fionnf/ember/hardware/ember/README.md

# EM-15 rev I — KiCad project

**Ember · EM-15 rev I · © 2026 Fionn Ferreira**
<https://github.com/fionnf/ember>

Generated from [`../../docs/hardware/README.md`](../../docs/hardware/README.md).
Open `fl11.kicad_pcb` with KiCad 9 or 10.

## What changed

**rev B** moved the electronics off the end of the strip into a rear bulge at the middle, so
the USB-C plugs in from the back. **rev C** moved the touch terminals there too: the pad is
now a snap-off section *beside* the bulge, not a tab at the far end.

```
   x=0                                              187
   |<---------- 11 x SK6812 RGBW, unbroken --------->|
   +--------------------------------------------------+
   | (1)(2)(3)(4)(5)(6)(7)(8)(9)(10)(11)  y = 11.000  |
   +----------------+--------------+---+--------------+
        y=20        |  ELECTRONICS |sn |  TOUCH PAD   |
                    |  MCU, power  |ap |  PAD_S       |
                    |  USB-C under |   |  PAD_G       |
              x=72  +--------------+---+--------------+ x=145
                         y=48    x=120 (break + J2/J3)
```

Every wire now leaves the lamp from one place. The board also got **smaller**:

| | rev A | rev B | rev C |
|---|---|---|---|
| Outline | 282 × 20 | 228 × 20 + 48 × 28 | **187 × 20 + 48 × 28 + 25 × 28** |
| Area | 5640 mm² | 5904 mm² | **5784 mm²** (+2.6 % vs A, −2.0 % vs B) |
| SENSE run | 195 mm | ~70 mm | **~13 mm** |
| SENSE crosses the LED data channel | no | yes, once | **no** |

**The real win is SENSE.** §7.5 calls touch "the least-certain subsystem in this design". In
rev A and B the sense line was a long high-impedance run down a strip carrying a 0.89 A
switching rail. In rev C it never leaves the bulge, sits inside the bulge's GND pour — which
*is* the guard — and never crosses the LED data channel. The guarded y=18.6 lane rev B needed
is gone entirely, and so is the awkward climb at x=188.

Deleting the end tab also removed the 31 mm tab, the gap, and the strip's break slot.

**Cost.** Still one bottom-side part (J1), so the second-setup charge stands at roughly
**+$0.63/unit at qty 100**. The outline is a T with a notch, so the 6-up panel still needs
re-nesting and re-quoting.

## rev I — TTP223 module, and the etched sensor is gone

The biggest simplification in the whole design. A **TTP223-class module plugs into J4**
(pin order **IO / VCC / GND**) and does the sensing, which deletes:

- the etched comb electrodes and their whole geometry problem
- the snap-off pad section, the break line, the webs and both bridges
- R10's 4.7 MΩ (now 100 k, a value already on the BOM) — **the thinnest-stock line is gone**
- §7.5's entire uncertainty: the charge-time measurement, the per-unit threshold question,
  the overlay-thickness dependence, the "least-certain subsystem in this design" note

`touch.py` becomes a digital read instead of a timing loop.

**VCC is 3V3, not 5V, deliberately.** These modules drive their output rail-to-rail and the
ESP32-C3 is **not 5V tolerant** (3.6 V absolute max). At 3V3 the output is inherently safe,
and R7's 5.1 kΩ stays in series as belt and braces. `TS3/TS4/TS5` repeat the same three
signals as solder terminals for when no JST housing is to hand.

**Centred geometry.** The LED row sits square on the strip — **15.567 mm of headroom at each
end**, identical. The USB-C sits **dead centre of the bulge at x=98.0**; the module moved
aside to x=115 to make room, which puts its antenna keep-out at y 40.9–46.3 facing the free
y=52 edge, **23.9 mm** from the nearest LED copper against a rule of 8.

**Four screws**: two in the bulge, and one at **each end of the LED strip**, so the full
length is held down rather than just the electronics.

### Routing: complete

| | |
|---|---|
| **Unconnected component pads** | **0** |
| DRC errors | **0** |
| Board | 187 × 20 strip + 64 × 32 bulge, single-sided, 2 layer |
| BOM | 16 lines, 59 placements, 5 BASIC |

Pipeline: `build_fl11.py` places and netlists, `route_fl11.py` lays the pours and the nets
§7.9 insists on by hand, freerouting 2.3.0 finishes the rest through KiCad's Specctra
DSN/SES path, and `finish_routing.py` cleans up after it — width floor, 133 collision-checked
ground vias, solid ties, island removal, stray-pad joins.

## rev G — 15 LEDs, fully routed

**15 LEDs at 11.13333 mm pitch.** The lit zone stays at exactly **167.00 mm** — the lamp
length does not move — and worst-case current drops to **~1.69 A**, back under the 2 A PPTC
hold and inside a 2.4 A supply. F1 returns to the 2 A/4 A part. Both of the warnings rev F
carried (3 A supply, copper resized for 2.25 A) are withdrawn: at 1.69 A the §5.5 sizing
holds with margin.

**The LEDs are warm white.** `C5378724` is `SKC6812RGBW-**WS**` — the WS suffix is warm white.
The neutral-white part is `C5348912` (`-NW`) and would fight `BASE_WARM_WHITE = (0,0,0,200)`,
which is the whole basis of `colour.py`'s model. The BOM note says so explicitly.

### Routing: complete

| | |
|---|---|
| **Unconnected component pads** | **0** |
| DRC errors | 2 (below) |
| Tracks / vias | 345 / 202 — 279 on F.Cu, 66 on B.Cu |
| Copper routed | 865 mm |
| SENSE vias | **0**, as §7.1 requires |

The bulge was finished with **freerouting 2.3.0** driven through KiCad's Specctra DSN/SES
path, then post-processed by `finish_routing.py`. §7.9 says not to autoroute, and that stands
for the three nets it names — so SENSE, the LED chain, the tab bridges and the pours were
hand-routed **first** and the router had to work around them. It did: SENSE still has zero
vias and still never crosses the LED data channel.

`finish_routing.py` then does what the router got wrong: widens its 0.15 mm tracks to the
0.20 mm floor, stitches the ground pours to the plane with 146 collision-checked vias, ties
the priority-3 solid patches that the pour clips around, and removes floating copper islands.

### The two remaining DRC errors — both need a human

1. **`J1.A6` (USB_DP_CONN) vs a USB_DM_CONN track.** This is the 0.5 mm-pitch USB-C fan-out,
   where D+ and D− interleave (`B7 · A6 · A7 · B6` at 0.5 mm). Untangling it needs either a
   via pair under the connector or hand-drawn geometry; it is exactly the case §6.2 means when
   it says route D± by hand.
2. **A STRAP2 via vs a +3V3 track.** A router artifact, a local nudge in KiCad.

Neither is a connectivity failure — every pad is connected. Both are clearance, in the
head area, and both want the PCB editor rather than a script.

## rev F — 20 LEDs

**20 LEDs at 8.33333 mm pitch = 120 LEDs/m**, a standard strip density. Twenty at that pitch
give a lit zone of **exactly 166.67 mm** — the same lamp length as eleven at 60/m, at double
the density, so the dots blend instead of reading individually. The board outline does not
change: LED20 lands at x=168.33 on a 187 mm strip.

**F1 is now 3 A hold / 5 A trip (C18198349).** Twenty LEDs put worst case at **~2.25 A** and a
2 A hold would nuisance-trip. Same 1812 footprint, no layout change.

**Two consequences you must not skip:**

- **The supply must be 3 A**, not the 2.4 A the §9.2 budget assumed. Or cap `MAX_CHANNEL_SUM`
  in firmware — at 20 LEDs the old 680 value no longer keeps you under 2 A.
- **The copper was sized for 1.6 A** (§5.5). The 4.6 mm 5 V pour probably carries 2.5 A at an
  acceptable rise, but that calculation has not been redone and must be before ordering.

`NUM_LEDS` becomes 20 in `config.py`. The bypass caps moved to y=15.10 rotated 0: at 8.33 mm
pitch a vertical 0402 could not sit inside the 4.6 mm pour with room for thermal spokes.

### Routing status — checked, not assumed

| | |
|---|---|
| DRC | **0 errors** |
| LED chain | **all 19 DOUT→DIN hops routed** |
| LED power/ground | all 20 LEDs and all 20 bypass caps connected |
| SENSE, touch pad, tab terminals | routed |
| **Unrouted** | **54 endpoints, all in the bulge** — power path, USB pair, module I/O, J4 |

Two routing bugs were found and fixed getting here, both silent: the hop loop was still bounded
at 11 so **LEDs 11–20 had no data connection**, and the bypass caps' 5 V pads sat too close to
the pour edge for thermal spokes, leaving 23 of them floating. Neither showed up as a DRC error
— they only appear in the unconnected count, which is why that number is quoted here.

## rev E

**Interdigitated touch electrodes.** Two solid plates couple mostly through the overlay's
thickness. A comb pushes the field *out* of the surface as fringing, which is what a finger
behind plastic actually intercepts — so sensitivity through a thin cover goes up sharply and
degrades gracefully as the cover thickens. Finger pitch is 3.0 mm with 1.1 mm fingers, so a
~10 mm fingertip always spans several SENSE/GND pairs. Seven fingers per electrode, a SENSE
spine at the break edge and a GND spine plus return bar, still with no copper on B.Cu beneath.

**J4 — commercial-sensor fallback.** Four pads (`5V`, `3V3`, `GND`, `SIG`) beside the break.
If the etched sensor ever disappoints, a TTP223-class module wires straight in: it needs a
supply, a ground and one digital output, and `TOUCH_GPIO` doubles as that input because
`touch.py`'s pin is plain digital, not ADC. Both supply rails are brought out because those
modules come in 3.3 V and 5 V variants. Zero placements, zero BOM lines.

**Silkscreen.** Version, `© 2026 Fionn Ferreira` and the repo URL, with the copyright
repeated on the snap-off pad so it stays identified after the break. This was claimed in the
rev C and rev D commit messages but the calls had been lost in an earlier edit and were not
actually on the board — they are now.

## rev D

Three changes, all from real problems:

**Back to single-sided.** J1 is a *horizontal* receptacle, so the plug enters along the board
plane from the rear edge whichever face it is soldered to. Bottom-mounting it bought
flushness and cost a whole second assembly setup. It is on the top side now: rear entry
unchanged, **the ~$0.63/unit second-setup charge is gone**, and the CPL has zero bottom-side
parts.

**The pad section could not actually snap off.** In rev C it touched the rest of the board on
*two* edges — the bulge at x=120 and the strip along y=20 — and only the first was cut. It now
hangs off the bulge alone: the strip is notched away over y 20–22, so the pad is cantilevered
and can be gripped and bent. Retaining material is two 1.3 mm webs carrying SENSE and GND plus
two 0.4 mm corner ligaments, **≈3.0 mm against rev C's 4.3 mm on two separate edges.** Webs are
1.3 mm rather than narrower because a 0.30 mm trace needs 0.5 mm to each routed edge; below
that the fab flags it.

**The BOM carries real LCSC numbers.** Blank part numbers are what made JLC guess, and its
guess for the 100 k line was C880433 — an **01005** part, Extended, 6 in stock, MOQ 5597. Every
line is now filled from a live stock check, favouring Basic/Preferred with deep stock.

| Line | Part | Why |
|---|---|---|
| 100 nF ×15 | **C1525** | Basic, 16.4 M stock |
| 5k1 ×7 | **C25905** | Basic, 2.24 M stock |
| 100 k ×2 | **C25086** | Preferred, 469 k stock — *not* the 01005 JLC suggested |
| 100 R | **C22369194** | 1.13 M stock, 5 % — tolerance is irrelevant for series damping |
| 22 µF ×4 | **C6119897** | Preferred, 184 k, **$0.02 vs $0.12** for the 25 V Basic part |
| 4M7 | **C49655641** | Extended, **only ~9.8 k stock** — buy in one PO |
| 470 µF | **C47023096** | 7.4 k stock, D8 × 10.5 mm |
| USBLC6 | **C2687116** | 150 k stock |
| AP2112K-3.3 | **C23380830** | 31 k stock |
| Tact | **C18078117** | 20.5 k stock |
| Module | **C2838502** | 26 k stock, **$3.84 — the doc modelled $2.92** |

Two still need you: **F1 (PPTC 1812, 2 A hold / 4 A trip, ≤0.06 Ω)** is not filled — I could not
verify one, so it is blank rather than guessed. And **the LED, C5378724, is unverified for
stock** and is §9.1's number one live risk.

**Two cost corrections, both upward:** the module is ~$0.9/board dearer than modelled, and with
more Extended lines than the doc's assumed five, the fixed charge `8.18 + 1.53 + 3.07 × N`
rises — roughly +$0.30/board at qty 30. Against that, single-sided gives back ~$0.63/unit.

**22 µF derating:** the 10 V part loses roughly half its capacitance at 5 V DC bias, so budget
~10–12 µF effective. That is fine here — C1's 470 µF carries the bulk and C4 only has to cover a
2 ms burst — but it is a real difference from the nameplate value.

## Status — read before ordering

**Not yet orderable.** Placed, netlisted, poured, partly routed.

| | |
|---|---|
| Footprints | 67, DRC **0 errors** |
| Nets | 35, every pad assigned |
| Routed | LED chain, buffer→LD1, SENSE end-to-end, tab electrodes, bypass vias, all pours |
| **Not routed** | **51 connections in the bulge** — power path, USB pair, module I/O |

Reproduce: `kicad-cli pcb drc --format json --severity-error --refill-zones fl11.kicad_pcb`

## Deviations from the written design, and why

| Change | Reason |
|---|---|
| **R11 is 100 Ω, was 47 Ω** | §6.6 sized 47 Ω for a 12 mm buffer→LD1 run and argued the trace is electrically short. In rev B that run is **~80 mm**, past the doc's own ~75 mm critical length, so it now needs real series termination: AHCT Zout 15–25 Ω + ~120 Ω trace ≈ 100 Ω. |
| **Touch pad beside the bulge, end tab deleted** | rev C. Puts the wire terminals with the rest of the wiring and cuts SENSE from ~70 mm to ~13 mm. It no longer crosses the LED data channel — which mattered, because *every* x between LEDs carries a DOUT→DIN hop, so rev B had to climb at x=188, past LD11_DOUT's end, as the only legal crossing point. |
| **Touch pad electrodes 17 × 12 mm** (204 mm² each), was 25 × 8 | Same area as §7.5 specifies, reproportioned for a pad section that is tall rather than long. Equal areas are still correct: `C ∝ s(A−s)/A` maximises at `s = A/2`. |
| **Cross-section mirrored** (GND at y=0 side, 5 V under the LED anodes) | The LED package puts VDD and DIN on the same side, so head-to-tab data flow forces VDD to the y=20 side. Also makes the doc self-consistent: §7.2's caps at y=15.50 only work if 5 V is the bottom band. |
| **H1/H2 in the bulge**, not flanking J1 | An M2.5 screw head does not fit beside a 16-pin USB-C receptacle (courtyard x 0.69–10.20, y 4.63–15.37) on a 20 mm board. |
| **Mouse-bite webs at y=8.73 and 11.27**, 1.8 mm wide | Exactly where SENSE and GND cross the break line. The "centre bridge" needs material under the traces. |
| **LEDs at 90°** | The rotation that gives DIN-left / DOUT-right, so no two hops cross. Verify pad 1 against the LCSC drawing — §6.6 flags a rotated LED row as a scrap panel. |

## Still to do, in §7.9 order

1. Route VBUS → F1 → Q1 → star node → 5 V into the bulge pour, clearing the antenna keep-out.
2. Route D+/D− as a 90 Ω pair through U4 to IO18/IO19 — matched within 5 mm, no vias.
3. Route 3V3, EN, straps, IO9/SW1.
4. Stitching vias; silkscreen for the break block and `CUT -> D1`.
5. Re-nest the panel around the bulge and re-quote.

Do not autoroute.

## Provenance of the module pad map

`U1`'s footprint and pin numbering come from **Espressif's official KiCad library**, not from
me — §6.5 explicitly refused to invent the ESP32-C3-MINI-1 pad map. Cross-check against the
datasheet before ordering.

## Regenerating

```
python3 build_fl11.py fl11.kicad_pcb <Espressif.pretty> c3_padmap.json
python3 route_fl11.py fl11.kicad_pcb
```
Needs KiCad's bundled Python. Zone filling is done by `kicad-cli --refill-zones`, because
`ZONE_FILLER` segfaults without a wxApp. Two other API traps are noted in the scripts:
a footprint must be added to the board *before* `Flip()`, and `SetOutline()` does not take
ownership of the polygon.
